kirbyfrugia/appleii-bluetooth-joystick/schematic/schematic.kicad_sch

## KiCad design schematic/schematic.kicad_sch (2026-01-22)

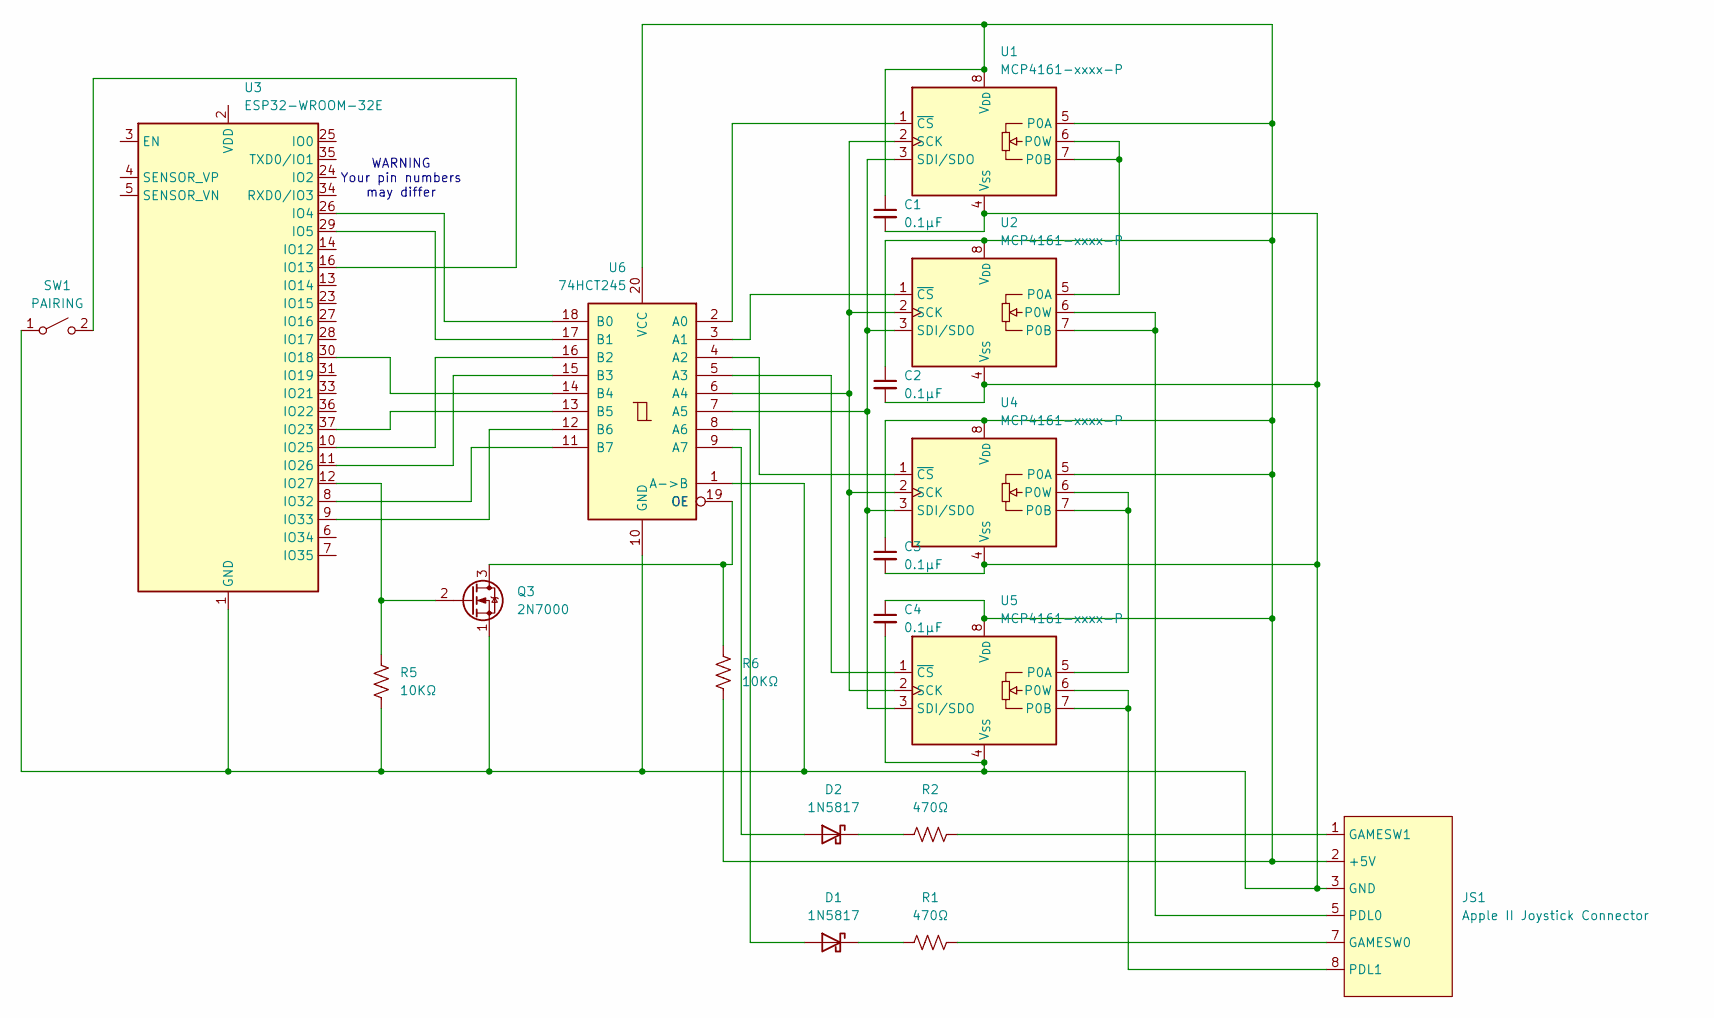
[picture p4: schematic schematic.kicad_sch]

Parts:
C1, C2, C3, C4: 0.1µF
D1, D2: 1N5817; D_DO-41_SOD81_P10.16mm_Horizontal
JS1: Apple II Joystick Connector
Q3: 2N7000; TO-92_Inline
R1, R2: 470Ω
R5, R6: 10KΩ
SW1: PAIRING
U1, U2, U4, U5: MCP4161-xxxx-P; DIP-8_W7.62mm
U3: ESP32-WROOM-32E; ESP32-WROOM-32D
U6: 74HCT245

Connections:
unnamed: C1.1, C2.1, C3.1, C4.1, JS1.2 (+5V), R6.2, U1.5 (P0A), U1.8 (V_{DD}), U2.8 (V_{DD}), U4.5 (P0A), U4.8 (V_{DD}), U5.8 (V_{DD}), U6.20 (VCC)
unnamed: C1.2, C2.2, C3.2, C4.2, JS1.3 (GND), Q3.1 (S), R5.2, SW1.1 (A), U1.4 (V_{SS}), U2.4 (V_{SS}), U3.1 (GND), U3.15 (GND), U3.38 (GND), U3.39 (GND), U4.4 (V_{SS}), U5.4 (V_{SS}), U6.1 (A->B), U6.10 (GND)
unnamed: D1.1 (K), R1.1
unnamed: D1.2 (A), U6.8 (A6)
unnamed: D2.1 (K), R2.1
unnamed: D2.2 (A), U6.9 (A7)
unnamed: JS1.1 (GAMESW1), R2.2
unnamed: JS1.5 (PDL0), U2.6 (P0W), U2.7 (P0B)
unnamed: JS1.7 (GAMESW0), R1.2
unnamed: JS1.8 (PDL1), U5.6 (P0W), U5.7 (P0B)
unnamed: Q3.2 (G), R5.1, U3.12 (IO27)
unnamed: Q3.3 (D), R6.1, U6.19 (CE)
unnamed: SW1.2 (B), U3.16 (IO13)
unnamed: U1.1 (~CS), U6.2 (A0)
unnamed: U1.2 (SCK), U2.2 (SCK), U4.2 (SCK), U5.2 (SCK), U6.6 (A4)
unnamed: U1.3 (SDI/SDO), U2.3 (SDI/SDO), U4.3 (SDI/SDO), U5.3 (SDI/SDO), U6.7 (A5)
unnamed: U1.6 (P0W), U1.7 (P0B), U2.5 (P0A)
unnamed: U2.1 (~CS), U6.3 (A1)
unnamed: U3.8 (IO32), U6.11 (B7)
unnamed: U3.9 (IO33), U6.12 (B6)
unnamed: U3.10 (IO25), U6.16 (B2)
unnamed: U3.11 (IO26), U6.15 (B3)
unnamed: U3.26 (IO4), U6.18 (B0)
unnamed: U3.29 (IO5), U6.17 (B1)
unnamed: U3.30 (IO18), U6.14 (B4)
unnamed: U3.37 (IO23), U6.13 (B5)
unnamed: U4.1 (~CS), U6.4 (A2)
unnamed: U4.6 (P0W), U4.7 (P0B), U5.5 (P0A)
unnamed: U5.1 (~CS), U6.5 (A3)

Notes on the sheet:
WARNING Your pin numbers may differ
